Tympan/Tympan_Rev_F_Hardware/TympanCase/2025-0227_Tympan-Rev-F_Case_Solidworks_2023/TRUSS HEAD PHILLIPS SCREW_6-32_0188LG.SLDPRT

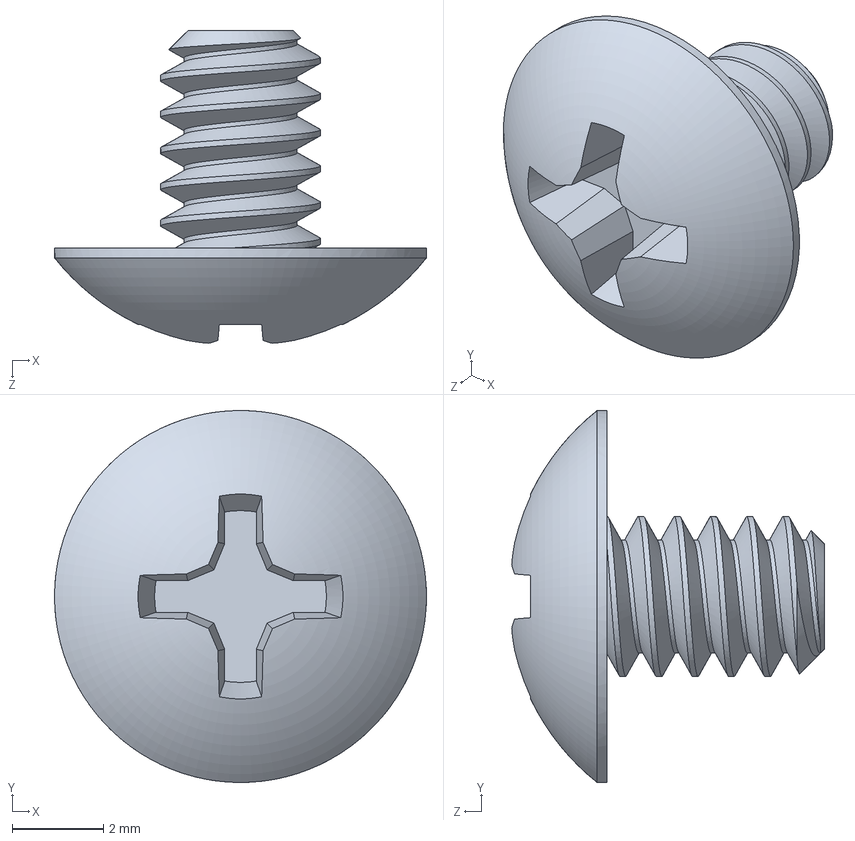
[picture p29: CAD file, 2025-02-27]
TympanCase/2025-0227_Tympan-Rev-F_Case_Solidworks_2023/TRUSS HEAD PHILLIPS SCREW_6-32_0188LG.SLDPRT
8.15 x 8.15 x 6.85 mm
