Tympan/Tympan_Rev_F_Hardware/TympanCase/2025-0227_Tympan-Rev-F_Case_Solidworks_2023/94180A321_HEAT-SET_INSERT_M2.5-045.SLDPRT

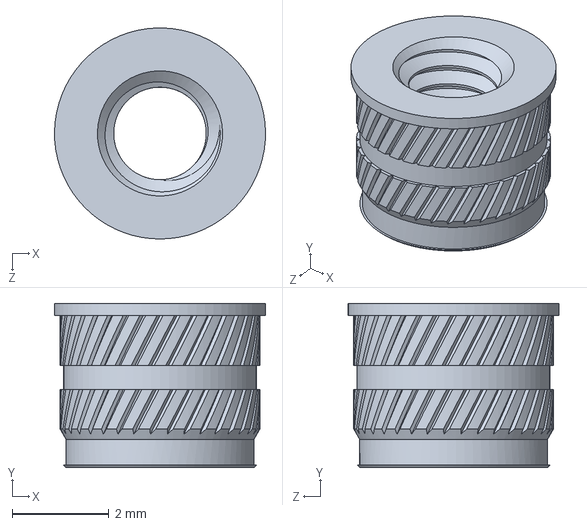
[picture p30: CAD file, 2025-02-27]
TympanCase/2025-0227_Tympan-Rev-F_Case_Solidworks_2023/94180A321_HEAT-SET_INSERT_M2.5-045.SLDPRT
4.37 x 3.40 x 4.37 mm
